ZeroPunchMan/freepad-f103/firmware/app/Application/app_info.c

#include "firmware_info.h"
#include "flash_layout.h"

#define MAJOR_VER_NUMBER (0)
#define MINOR_VER_NUMBER (0)
#define PATCH_VER_NUMBER (6)

const FirmwareInfo_t appFwInfo __attribute__((section(".ARM.__AT_0x08013800"))) = {
    .verMajor = MAJOR_VER_NUMBER,
    .verMinor = MINOR_VER_NUMBER,
    .verPatch = PATCH_VER_NUMBER,

    .check = FIRMWARE_CHECK_VALUE(MAJOR_VER_NUMBER, MINOR_VER_NUMBER, PATCH_VER_NUMBER, MINOR_VER_NUMBER, PATCH_VER_NUMBER),
};

// const int testData __attribute__((at(APP_START_ADDR + 38*1024))) = 0x12345;
