ZeroPunchMan/freepad-f103/firmware/common/button.h

#pragma once

#include "cl_common.h"

typedef enum
{
    BtnIdx_Pair = 0,
    BtnIdx_A,
    BtnIdx_Y,
    BtnIdx_Max,
} ButtonIdx_t;

typedef enum
{
    ButtonEvent_Down,      // 按下
    ButtonEvent_Click,     // 点击, 短按松开
    ButtonEvent_LongPress, // 长按
    ButtonEvent_LpUp,      // 长按松开
} ButtonEvent_t;

#define BUTTON_BOUNCE_TIME  (50)
#define BUTTON_LONG_PRESS_TIME  (2000)

void Button_Init(void);

void Button_Process(void);
