ZeroPunchMan/freepad-f103/firmware/boot/Core/Src/usart.c

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
/* Includes ------------------------------------------------------------------*/
#include "usart.h"

/* USART1 init function */

void MX_USART1_UART_Init(void)
{

  LL_USART_InitTypeDef USART_InitStruct = {0};

  LL_GPIO_InitTypeDef GPIO_InitStruct = {0};

  /* Peripheral clock enable */
  LL_APB2_GRP1_EnableClock(LL_APB2_GRP1_PERIPH_USART1);

  LL_APB2_GRP1_EnableClock(LL_APB2_GRP1_PERIPH_GPIOA);
  /**USART1 GPIO Configuration
  PA9   ------> USART1_TX
  PA10   ------> USART1_RX
  */
  GPIO_InitStruct.Pin = LL_GPIO_PIN_9;
  GPIO_InitStruct.Mode = LL_GPIO_MODE_ALTERNATE;
  GPIO_InitStruct.Speed = LL_GPIO_SPEED_FREQ_HIGH;
  GPIO_InitStruct.OutputType = LL_GPIO_OUTPUT_PUSHPULL;
  LL_GPIO_Init(GPIOA, &GPIO_InitStruct);

  GPIO_InitStruct.Pin = LL_GPIO_PIN_10;
  GPIO_InitStruct.Mode = LL_GPIO_MODE_FLOATING;
  LL_GPIO_Init(GPIOA, &GPIO_InitStruct);

  /* USART1 interrupt Init */
  NVIC_SetPriority(USART1_IRQn, NVIC_EncodePriority(NVIC_GetPriorityGrouping(),0, 0));
  NVIC_EnableIRQ(USART1_IRQn);

  USART_InitStruct.BaudRate = 115200;
  USART_InitStruct.DataWidth = LL_USART_DATAWIDTH_8B;
  USART_InitStruct.StopBits = LL_USART_STOPBITS_1;
  USART_InitStruct.Parity = LL_USART_PARITY_NONE;
  USART_InitStruct.TransferDirection = LL_USART_DIRECTION_TX;
  USART_InitStruct.HardwareFlowControl = LL_USART_HWCONTROL_NONE;
  USART_InitStruct.OverSampling = LL_USART_OVERSAMPLING_16;
  LL_USART_Init(USART1, &USART_InitStruct);
  LL_USART_ConfigAsyncMode(USART1);
  LL_USART_Enable(USART1);
  /* USER CODE BEGIN USART1_Init 2 */
  // LL_USART_EnableIT_TXE(USART1);
  /* USER CODE END USART1_Init 2 */

}

/* USER CODE BEGIN 1 */
#include "stdio.h"

CL_QUEUE_DEF_INIT(usart1SendQueue, 1024, uint8_t, );

FILE __stdout;


void _sys_exit(int x)
{
    x = x;
}

int fputc(int ch, FILE *f)
{
    uint8_t data = ch;
    CL_QueueAdd(&usart1SendQueue, &data);
    LL_USART_EnableIT_TXE(USART1);
    return ch;
}

/* USER CODE END 1 */
